thingSoC/TSOC_GROVEY_FOUR/TSOC_GROVEY_FOUR/eagleUp/eagleUp_TSOC_GROVEY_FOUR_board_top.jpg

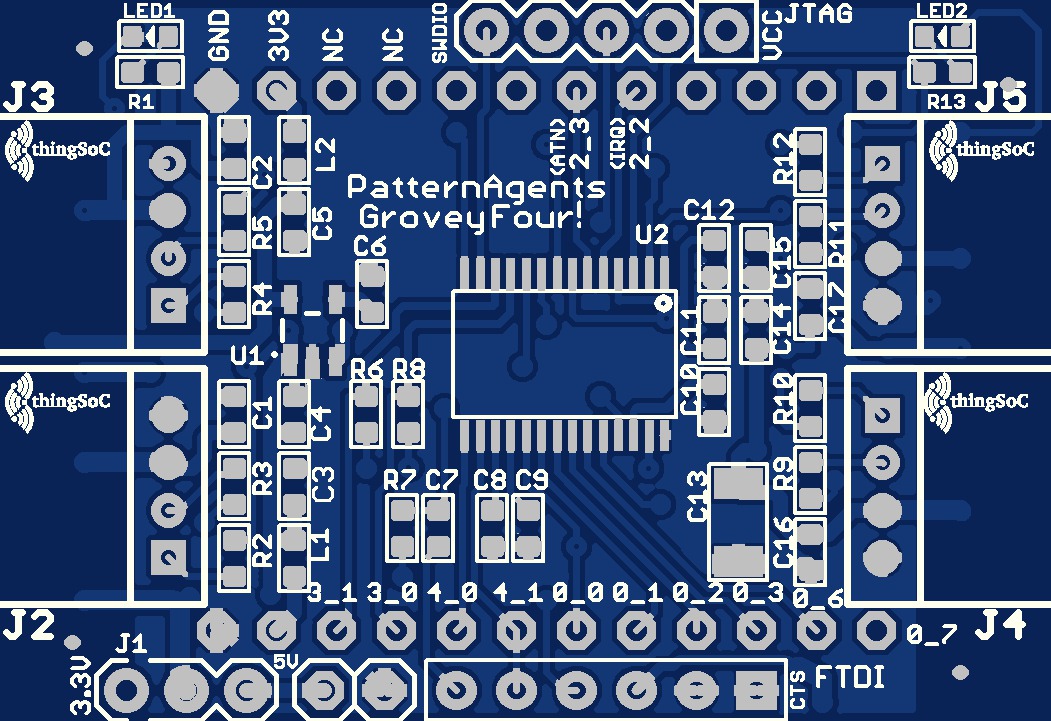
TSOC_GROVEY_FOUR/eagleUp/eagleUp_TSOC_GROVEY_FOUR_board_top.jpg
