thingSoC/TSOC_GROVEY_FOUR/TSOC_GROVEY_FOUR/images/TSOC_GROVEY_FOUR_iso.png

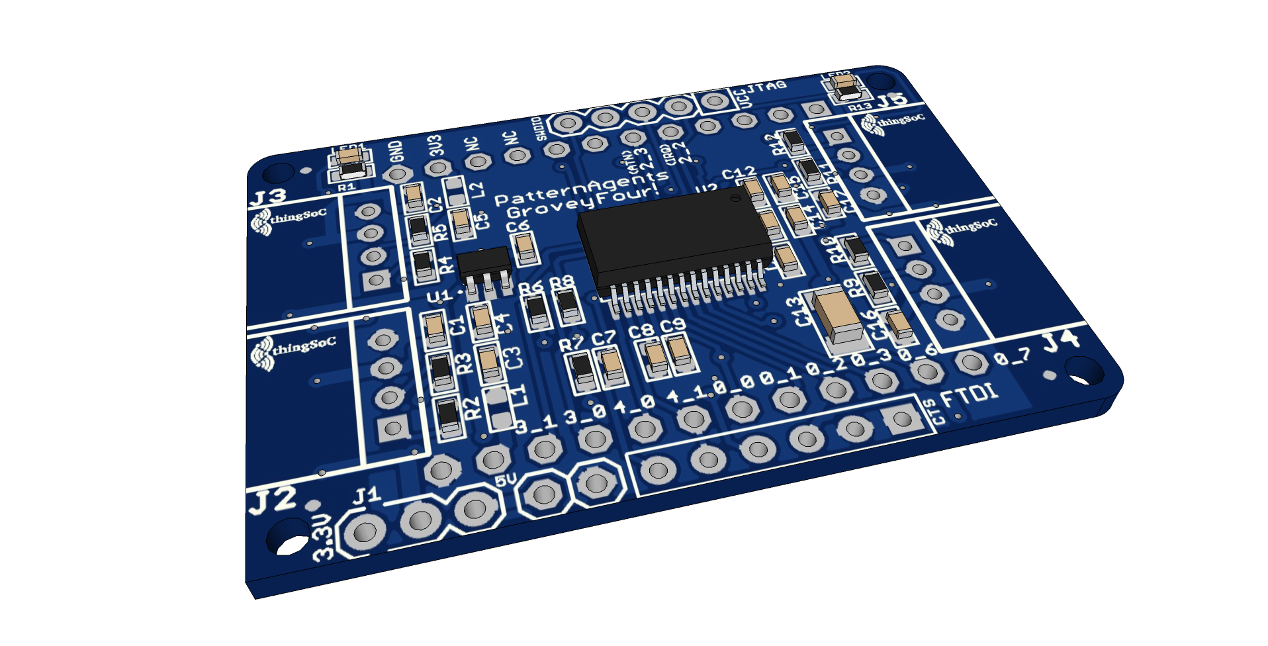
TSOC_GROVEY_FOUR/images/TSOC_GROVEY_FOUR_iso.png
