thingSoC/TSOC_GROVEY_FOUR/TSOC_GROVEY_FOUR/revisions/R1_0/images/TSOC_GROVEY_FOUR.png

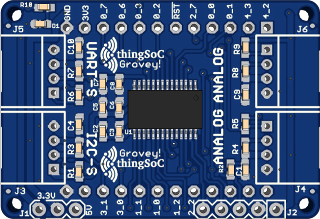
TSOC_GROVEY_FOUR/revisions/R1_0/images/TSOC_GROVEY_FOUR.png
