thingSoC/TSOC_GROVEY_FOUR/TSOC_GROVEY_FOUR/revisions/R1_0/TSOC_GROVEY_FOUR_sch.pdf

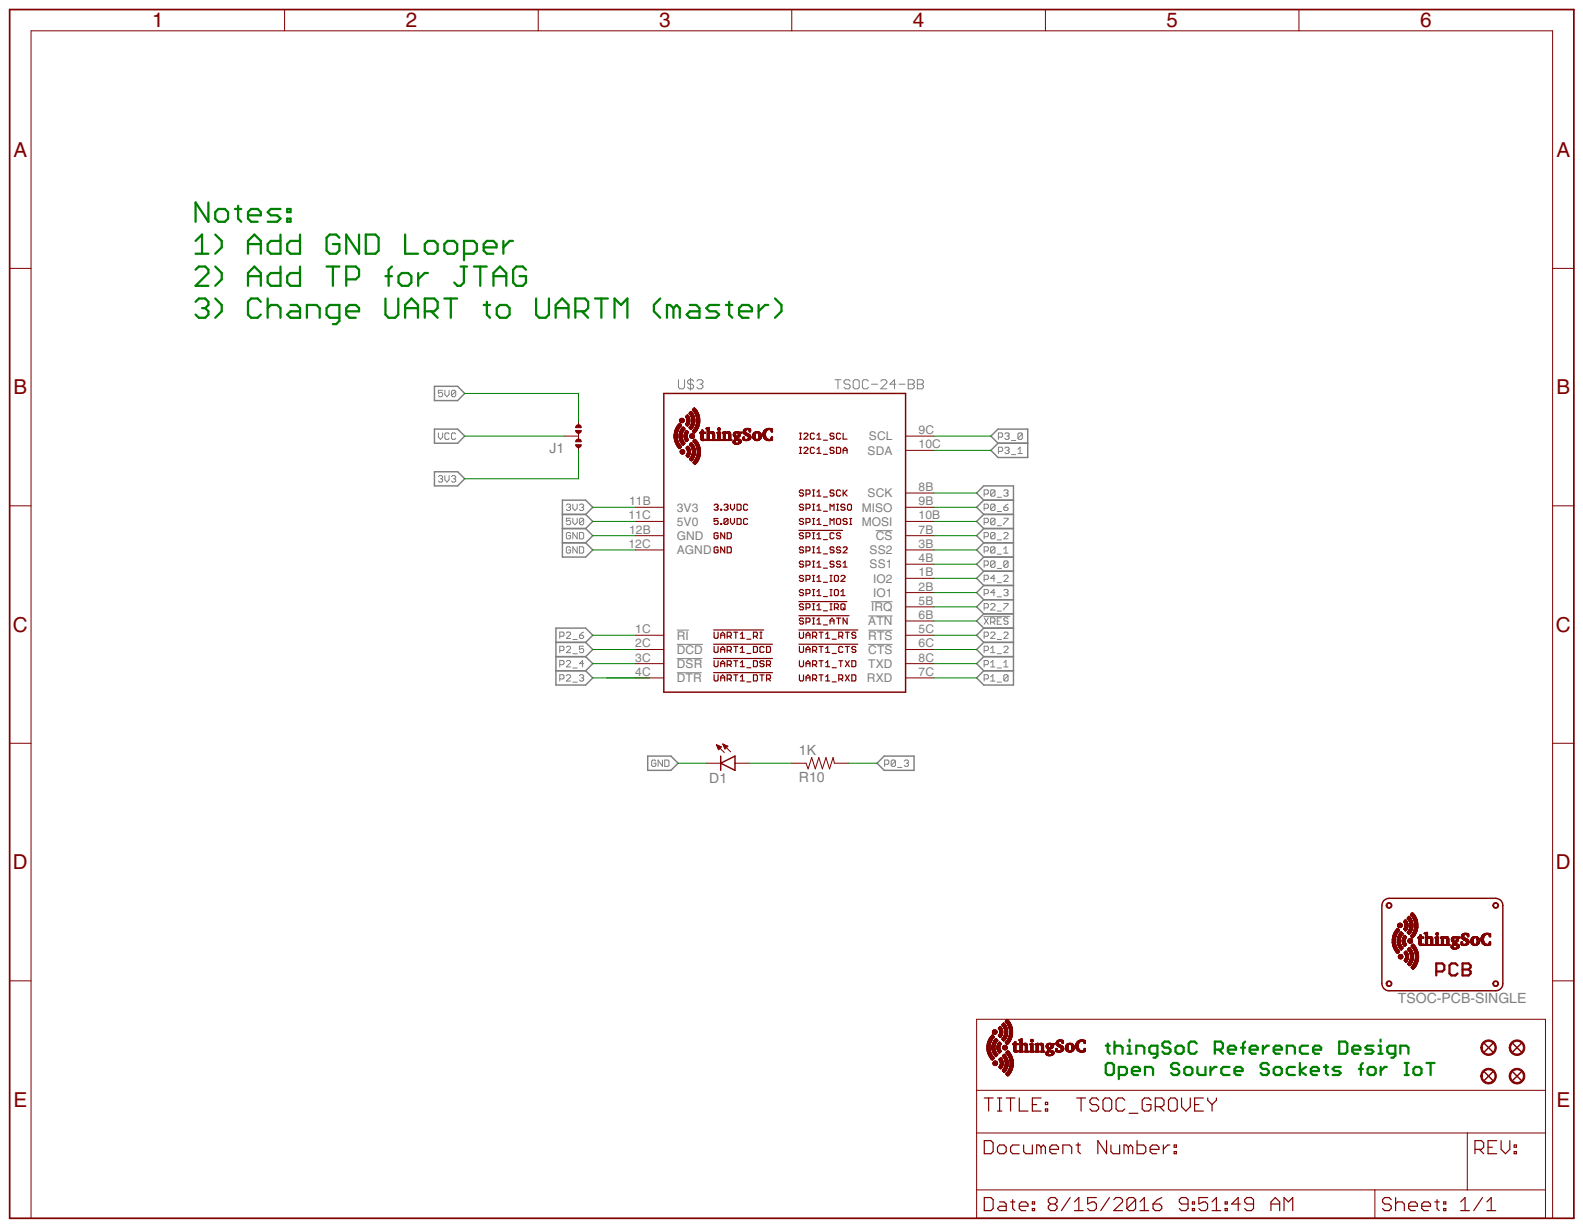
[picture p45: page 1]

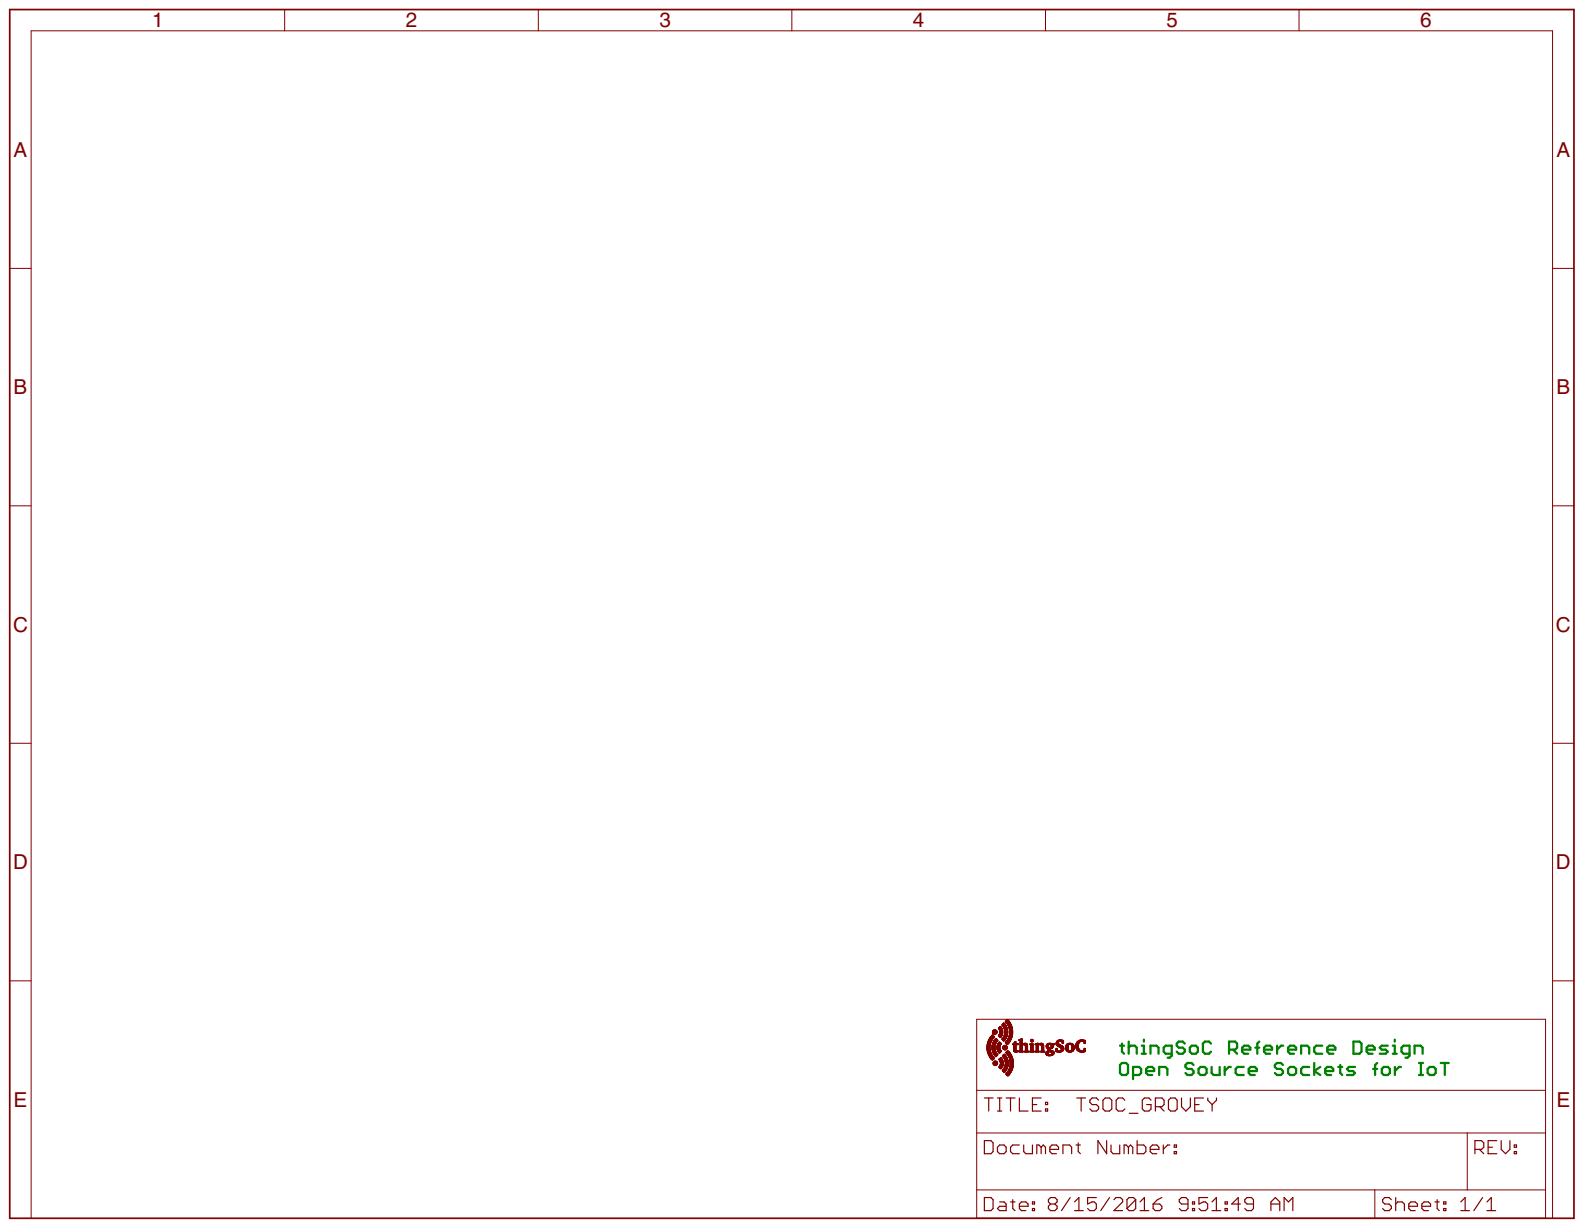
[picture p46: page 2]

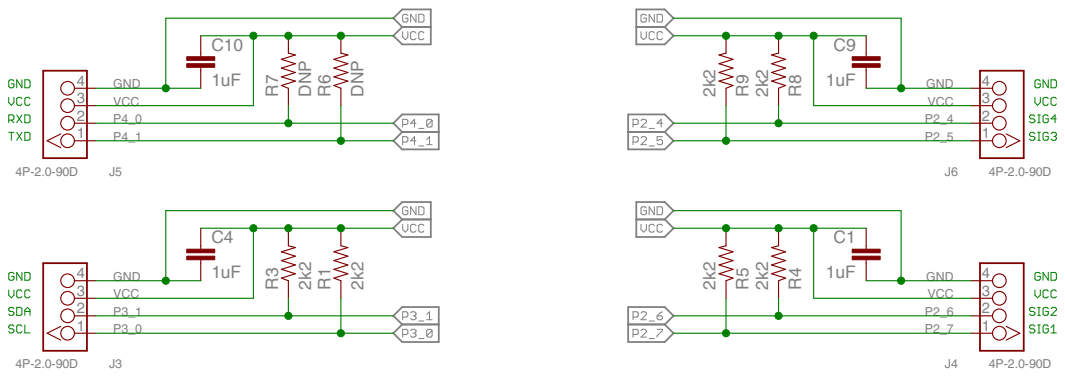
[picture p47: page 3]

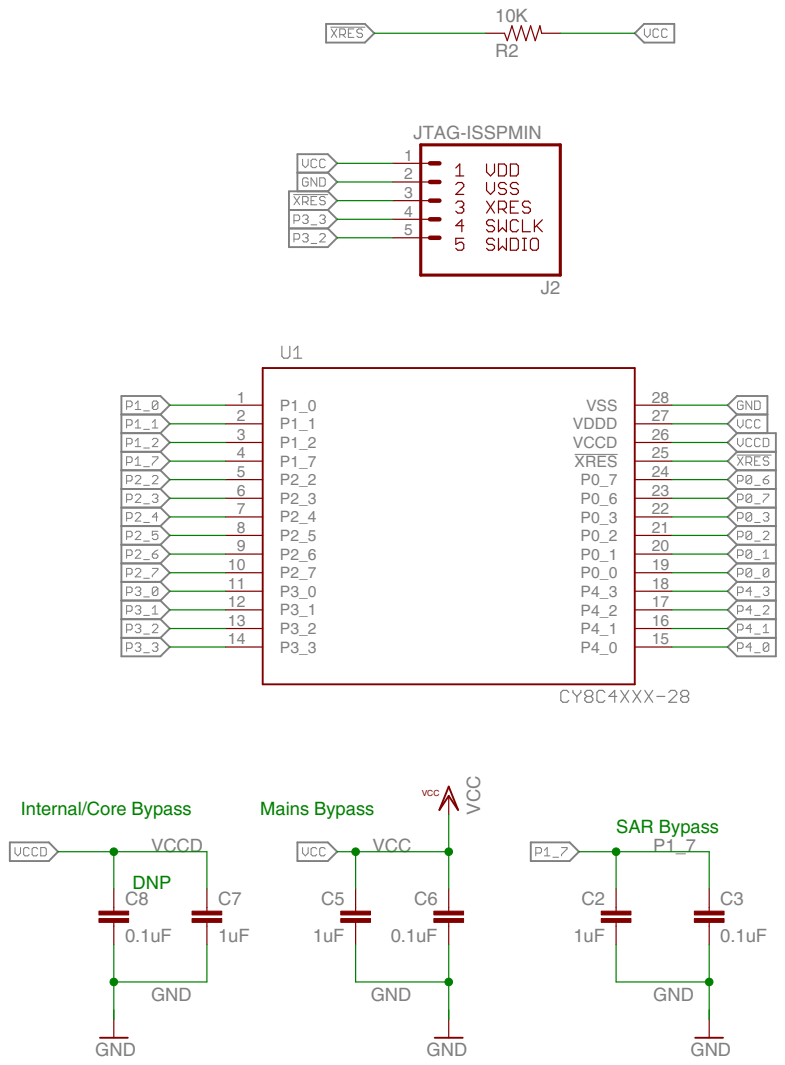
[picture p48: page 4]
