thingSoC/TSOC_GROVEY_FOUR/TSOC_GROVEY_FOUR/revisions/R1_0/TSOC_GROVEY_FOUR_sch_black.pdf

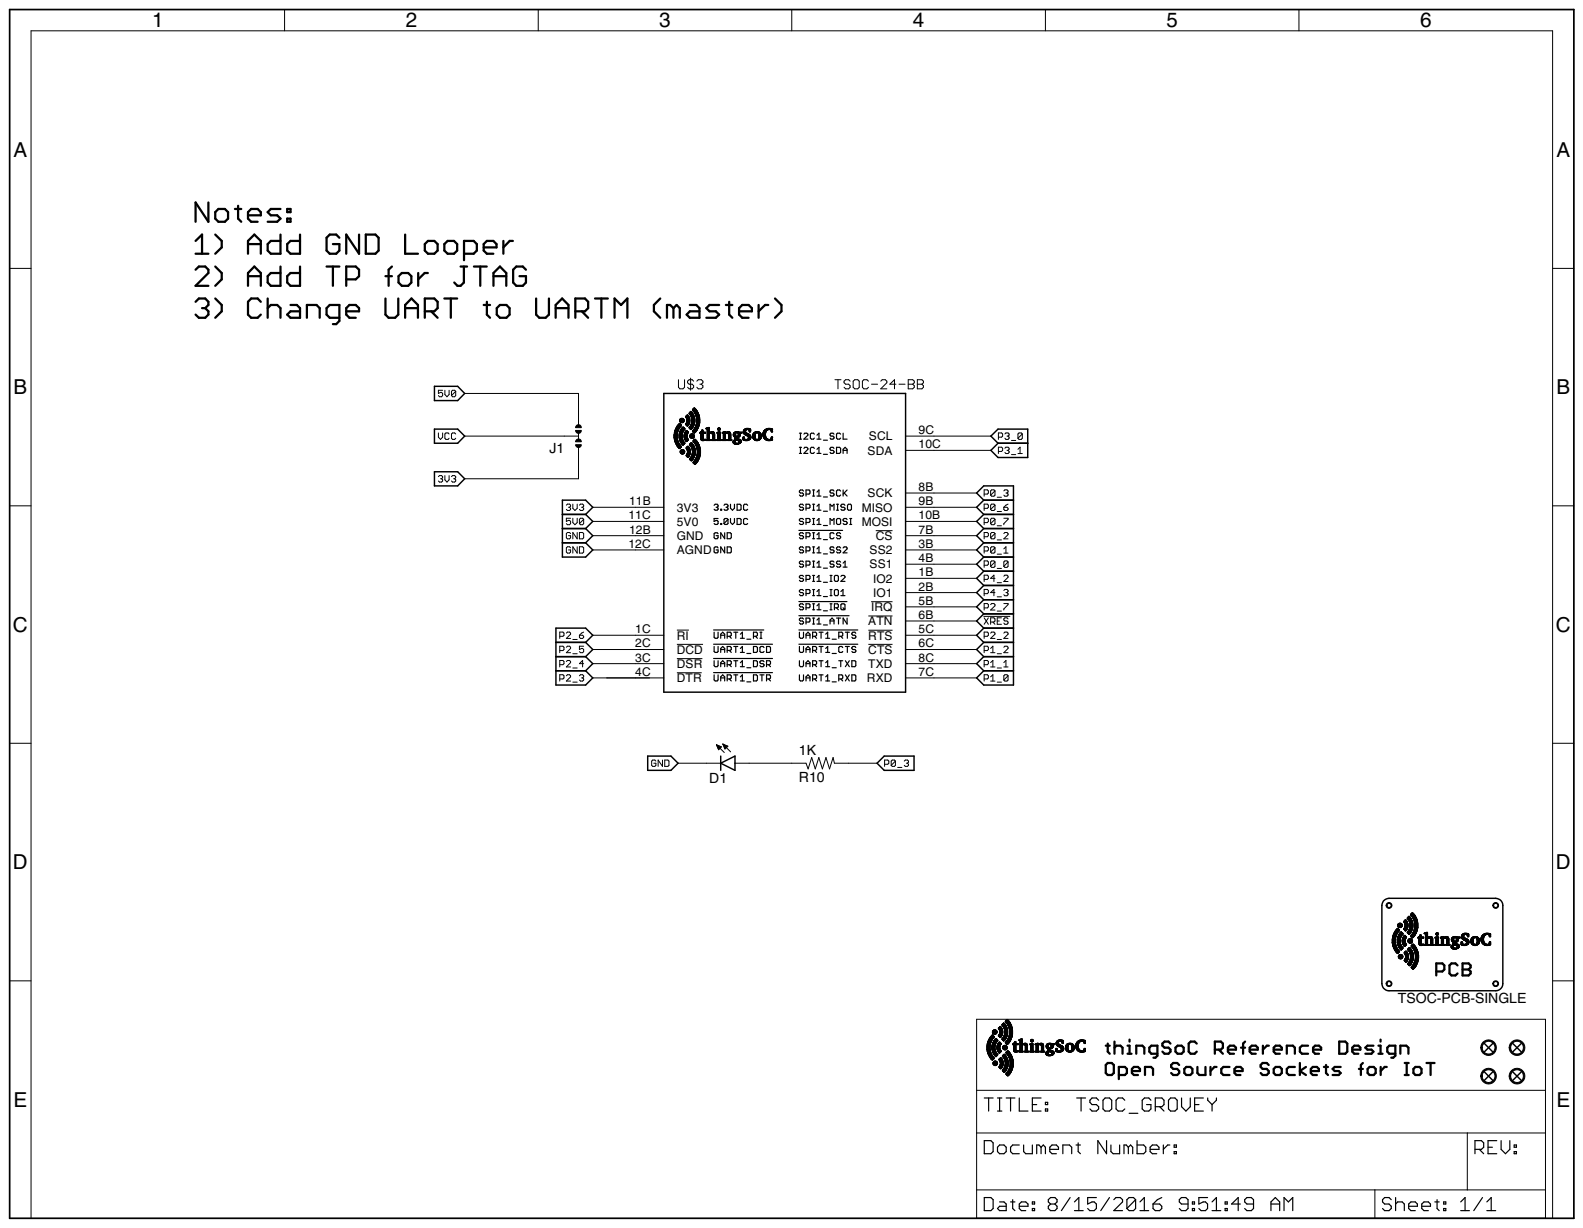
[picture p49: page 1]

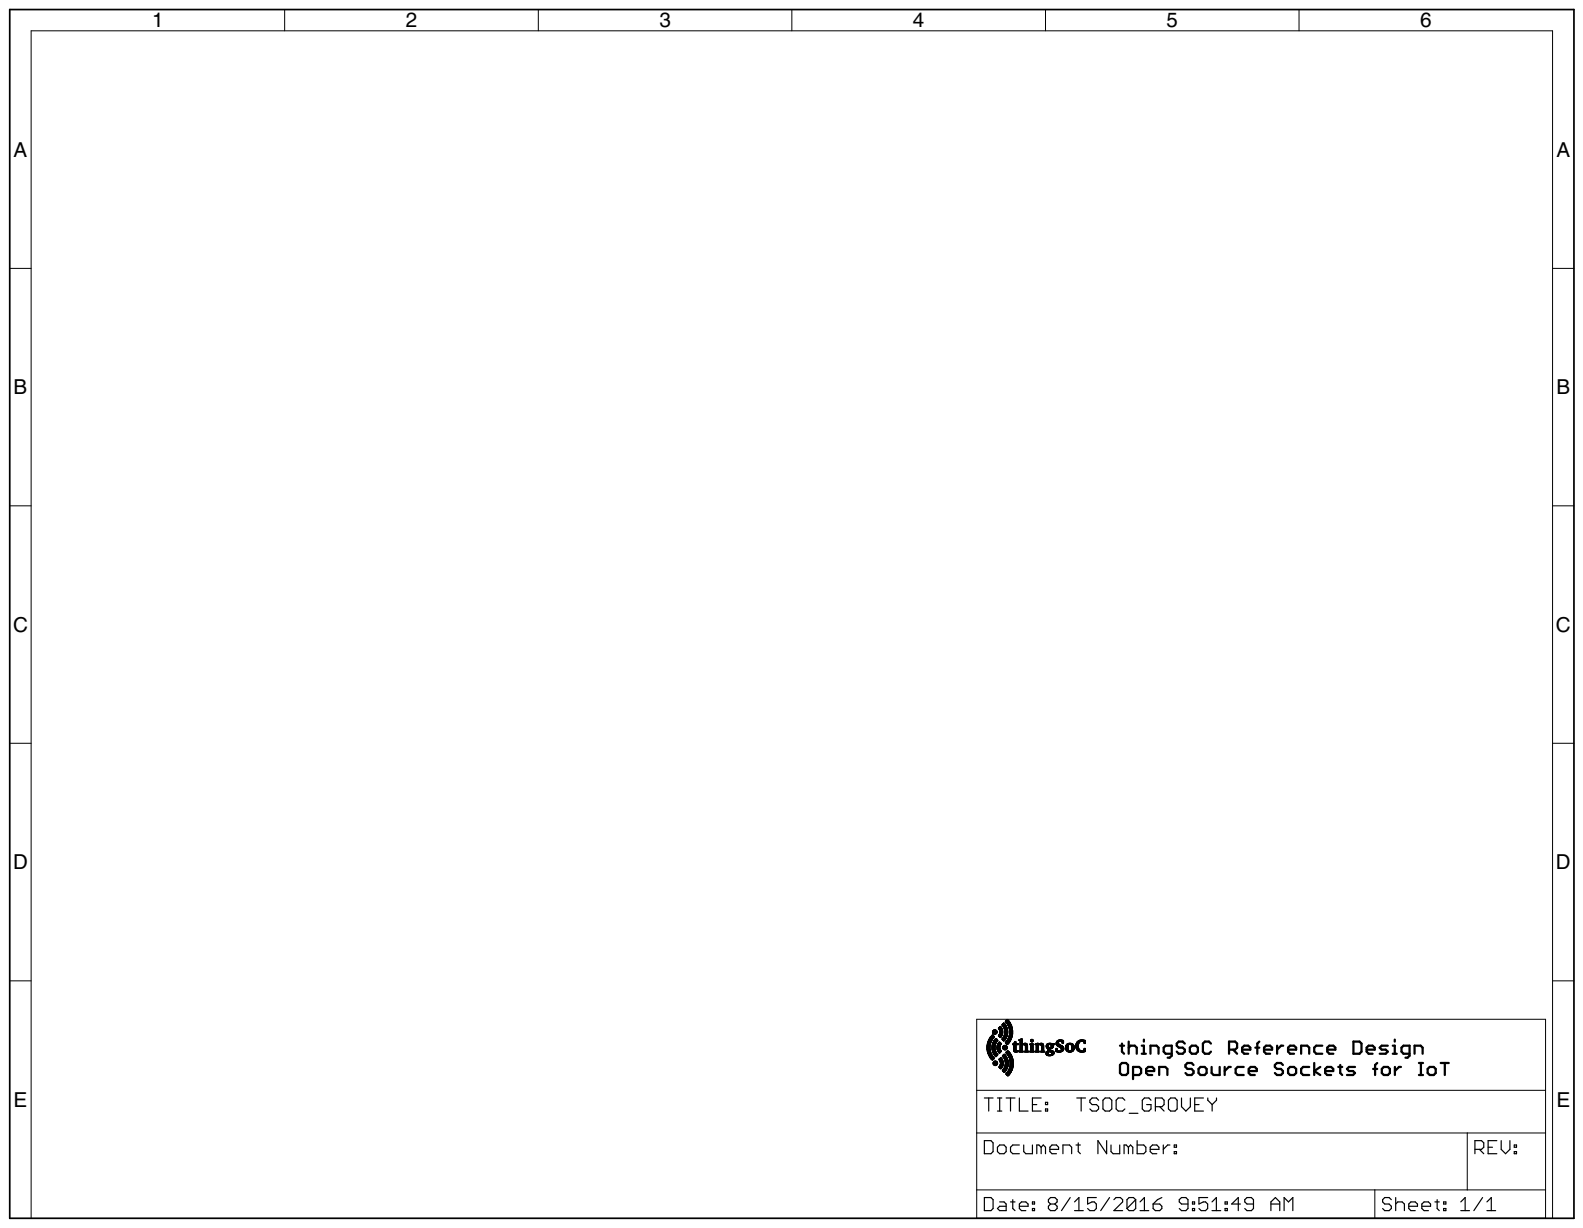
[picture p50: page 2]

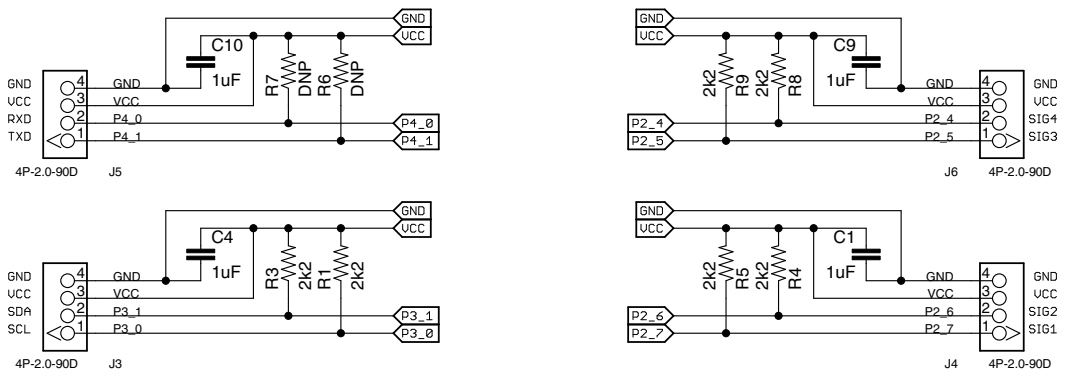
[picture p51: page 3]

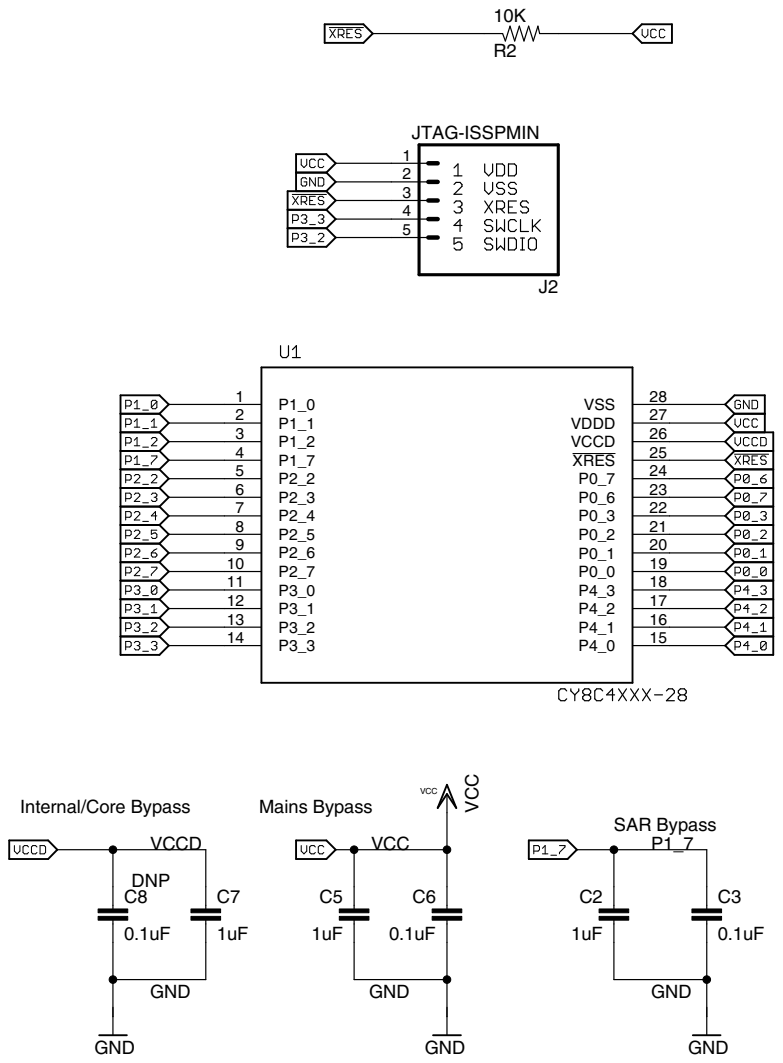
[picture p52: page 4]
