thingSoC/TSOC_GROVEY_FOUR/TSOC_GROVEY_FOUR/revisions/R1_0/TSOC_GROVEY_FOUR_tsilk.pdf

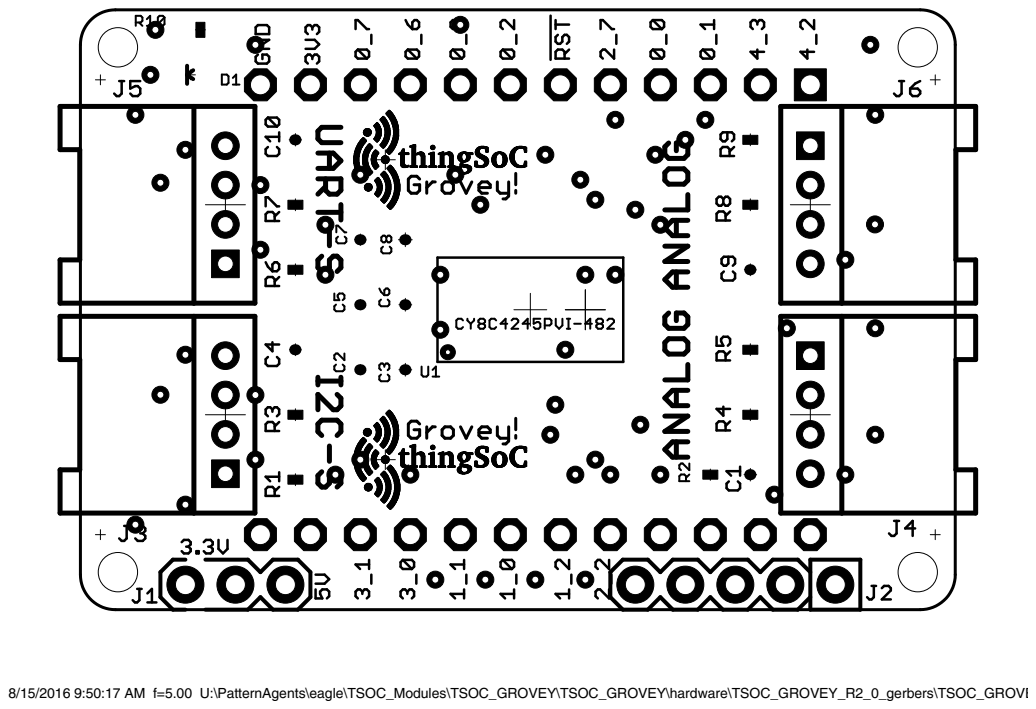
[picture p53: page 1]

8/15/2016 9:50:17 AM f=5.00 U:\PatternAgents\eagle\TSOC_Modules\TSOC_GROVEY\TSOC_GROVEY\hardware\TSOC_GROVEY_R2_0_gerbers\TSOC_GROVEY.brd
